nickschiffer/RoboARM/Schematics/Voltage Divider (x-axis).png

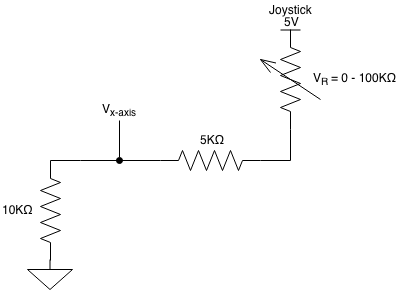
Schematics/Voltage Divider (x-axis).png
